MiSTer-devel/MiSTerLaggy_MiSTer/MiSTerLaggy.sv

//============================================================================
//
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
//============================================================================

module emu
(
	//Master input clock
	input         CLK_50M,

	//Async reset from top-level module.
	//Can be used as initial reset.
	input         RESET,

	//Must be passed to hps_io module
	inout  [48:0] HPS_BUS,

	//Base video clock. Usually equals to CLK_SYS.
	output        CLK_VIDEO,

	//Multiple resolutions are supported using different CE_PIXEL rates.
	//Must be based on CLK_VIDEO
	output        CE_PIXEL,

	//Video aspect ratio for HDMI. Most retro systems have ratio 4:3.
	//if VIDEO_ARX[12] or VIDEO_ARY[12] is set then [11:0] contains scaled size instead of aspect ratio.
	output [12:0] VIDEO_ARX,
	output [12:0] VIDEO_ARY,

	output  [7:0] VGA_R,
	output  [7:0] VGA_G,
	output  [7:0] VGA_B,
	output        VGA_HS,
	output        VGA_VS,
	output        VGA_DE,    // = ~(VBlank | HBlank)
	output        VGA_F1,
	output [1:0]  VGA_SL,
	output        VGA_SCALER, // Force VGA scaler
	output        VGA_DISABLE, // analog out is off

	input  [11:0] HDMI_WIDTH,
	input  [11:0] HDMI_HEIGHT,
	output        HDMI_FREEZE,
	output        HDMI_BLACKOUT,

`ifdef MISTER_FB
	// Use framebuffer in DDRAM
	// FB_FORMAT:
	//    [2:0] : 011=8bpp(palette) 100=16bpp 101=24bpp 110=32bpp
	//    [3]   : 0=16bits 565 1=16bits 1555
	//    [4]   : 0=RGB  1=BGR (for 16/24/32 modes)
	//
	// FB_STRIDE either 0 (rounded to 256 bytes) or multiple of pixel size (in bytes)
	output        FB_EN,
	output  [4:0] FB_FORMAT,
	output [11:0] FB_WIDTH,
	output [11:0] FB_HEIGHT,
	output [31:0] FB_BASE,
	output [13:0] FB_STRIDE,
	input         FB_VBL,
	input         FB_LL,
	output        FB_FORCE_BLANK,

`ifdef MISTER_FB_PALETTE
	// Palette control for 8bit modes.
	// Ignored for other video modes.
	output        FB_PAL_CLK,
	output  [7:0] FB_PAL_ADDR,
	output [23:0] FB_PAL_DOUT,
	input  [23:0] FB_PAL_DIN,
	output        FB_PAL_WR,
`endif
`endif

	output        LED_USER,  // 1 - ON, 0 - OFF.

	// b[1]: 0 - LED status is system status OR'd with b[0]
	//       1 - LED status is controled solely by b[0]
	// hint: supply 2'b00 to let the system control the LED.
	output  [1:0] LED_POWER,
	output  [1:0] LED_DISK,

	// I/O board button press simulation (active high)
	// b[1]: user button
	// b[0]: osd button
	output  [1:0] BUTTONS,

	input         CLK_AUDIO, // 24.576 MHz
	output [15:0] AUDIO_L,
	output [15:0] AUDIO_R,
	output        AUDIO_S,   // 1 - signed audio samples, 0 - unsigned
	output  [1:0] AUDIO_MIX, // 0 - no mix, 1 - 25%, 2 - 50%, 3 - 100% (mono)

	//ADC
	inout   [3:0] ADC_BUS,

	//SD-SPI
	output        SD_SCK,
	output        SD_MOSI,
	input         SD_MISO,
	output        SD_CS,
	input         SD_CD,

	//High latency DDR3 RAM interface
	//Use for non-critical time purposes
	output        DDRAM_CLK,
	input         DDRAM_BUSY,
	output  [7:0] DDRAM_BURSTCNT,
	output [28:0] DDRAM_ADDR,
	input  [63:0] DDRAM_DOUT,
	input         DDRAM_DOUT_READY,
	output        DDRAM_RD,
	output [63:0] DDRAM_DIN,
	output  [7:0] DDRAM_BE,
	output        DDRAM_WE,

	//SDRAM interface with lower latency
	output        SDRAM_CLK,
	output        SDRAM_CKE,
	output [12:0] SDRAM_A,
	output  [1:0] SDRAM_BA,
	inout  [15:0] SDRAM_DQ,
	output        SDRAM_DQML,
	output        SDRAM_DQMH,
	output        SDRAM_nCS,
	output        SDRAM_nCAS,
	output        SDRAM_nRAS,
	output        SDRAM_nWE,

`ifdef MISTER_DUAL_SDRAM
	//Secondary SDRAM
	//Set all output SDRAM_* signals to Z ASAP if SDRAM2_EN is 0
	input         SDRAM2_EN,
	output        SDRAM2_CLK,
	output [12:0] SDRAM2_A,
	output  [1:0] SDRAM2_BA,
	inout  [15:0] SDRAM2_DQ,
	output        SDRAM2_nCS,
	output        SDRAM2_nCAS,
	output        SDRAM2_nRAS,
	output        SDRAM2_nWE,
`endif

	input         UART_CTS,
	output        UART_RTS,
	input         UART_RXD,
	output        UART_TXD,
	output        UART_DTR,
	input         UART_DSR,

	// Open-drain User port.
	// 0 - D+/RX
	// 1 - D-/TX
	// 2..6 - USR2..USR6
	// Set USER_OUT to 1 to read from USER_IN.
	input   [6:0] USER_IN,
	output  [6:0] USER_OUT,

	input         OSD_STATUS,

	output        VIO_EN,
	output        VIO_STROBE,
	input  [15:0] VIO_DOUT,
	output [15:0] VIO_DIN,
	input  [15:0] VIO_CFG,

	input         HDMI_VBL
);

///////// Default values for ports not used in this core /////////

assign ADC_BUS  = 'Z;
assign {UART_RTS, UART_TXD, UART_DTR} = 0;
assign {SD_SCK, SD_MOSI, SD_CS} = 'Z;
assign {SDRAM_DQ, SDRAM_A, SDRAM_BA, SDRAM_CLK, SDRAM_CKE, SDRAM_DQML, SDRAM_DQMH, SDRAM_nWE, SDRAM_nCAS, SDRAM_nRAS, SDRAM_nCS} = 'Z;
assign {DDRAM_CLK, DDRAM_BURSTCNT, DDRAM_ADDR, DDRAM_DIN, DDRAM_BE, DDRAM_RD, DDRAM_WE} = '0;  

assign VGA_SL = 0;
assign VGA_F1 = 0;
assign VGA_SCALER  = 0;
assign VGA_DISABLE = 0;
assign HDMI_FREEZE = 0;
assign HDMI_BLACKOUT = 0;

assign AUDIO_S = 0;
assign AUDIO_L = 0;
assign AUDIO_R = 0;
assign AUDIO_MIX = 0;

assign LED_DISK = 0;
assign LED_POWER = 0;
assign BUTTONS = 0;

//////////////////////////////////////////////////////////////////

`include "build_id.v" 
localparam CONF_STR = {
	"MiSTerLaggy;;",
	"FC0,BIN,Load CPU ROM;",
	"-;",
	"T[0],Reset;",
	"J1,Ok,Back,Menu;",
	"jn,A,B,Start;",
	"V,v",`BUILD_DATE 
};

wire forced_scandoubler;
wire   [1:0] buttons;
wire [127:0] status;
wire  [10:0] ps2_key;
wire  [31:0] gamepad;

wire ioctl_download, ioctl_wr;
wire [15:0] ioctl_index, ioctl_dout;
wire [26:0] ioctl_addr;
wire new_vmode;

hps_io #(.CONF_STR(CONF_STR), .WIDE(1)) hps_io
(
	.clk_sys(clk_sys),
	.HPS_BUS(HPS_BUS),
	.gamma_bus(),

	.forced_scandoubler(forced_scandoubler),

	.buttons(buttons),
	.status(status),
	.status_menumask({status[5]}),

	.joystick_0(gamepad),
	
	.ps2_key(ps2_key),

	.ioctl_download(ioctl_download),
	.ioctl_wr(ioctl_wr),
	.ioctl_index(ioctl_index),
	.ioctl_addr(ioctl_addr),
	.ioctl_dout(ioctl_dout),
	.ioctl_wait(0),

	.new_vmode(new_vmode)
);

///////////////////////   CLOCKS   ///////////////////////////////

wire clk_sys;

wire [63:0] reconfig_to_pll;
wire [63:0] reconfig_from_pll;
wire        cfg_waitrequest;
reg         cfg_write;
reg   [5:0] cfg_address;
reg  [31:0] cfg_data;

pll pll
(
	.refclk(CLK_50M),
	.rst(0),
	.outclk_0(clk_sys),
	.reconfig_from_pll(reconfig_from_pll),
	.reconfig_to_pll(reconfig_to_pll)
);

pll_cfg pll_cfg
(
	.mgmt_clk(CLK_50M),
	.mgmt_reset(0),
	.mgmt_waitrequest(cfg_waitrequest),
	.mgmt_read(0),
	.mgmt_readdata(),
	.mgmt_write(cfg_write),
	.mgmt_address(cfg_address),
	.mgmt_writedata(cfg_data),
	.reconfig_to_pll(reconfig_to_pll),
	.reconfig_from_pll(reconfig_from_pll)
);

wire [5:0] pll_addr;
wire [31:0] pll_value;
wire pll_busy;
wire pll_write;

reg pll_fifo_rdack = 0;
wire [5:0] pll_cfg_addr;
wire [31:0] pll_cfg_value;
wire pll_fifo_empty;

pll_fifo pll_fifo(
	.wrclk(clk_sys),
	.wrreq(pll_write),
	.wrfull(pll_busy),
	.data({2'b00, pll_addr, pll_value}),

	.rdclk(CLK_50M),
	.rdreq(pll_fifo_rdack),
	.q({pll_cfg_addr, pll_cfg_value}),
	.rdempty(pll_fifo_empty)
);

always_ff @(posedge CLK_50M) begin
	cfg_write <= 0;
	pll_fifo_rdack <= 0;

	if (~cfg_waitrequest & ~pll_fifo_empty) begin
		cfg_write <= 1;
		cfg_address <= pll_cfg_addr;
		cfg_data <= pll_cfg_value;
		pll_fifo_rdack <= 1;
	end
end

wire reset = RESET | status[0] | buttons[1] | ioctl_download;

wire HBlank;
wire HSync;
wire VBlank;
wire VSync;

system system
(
	.clk(clk_sys),
	.clk_50m(CLK_50M),

	.reset(reset),

	.ce_pixel(CE_PIXEL),

	.HBlank(HBlank),
	.HSync(HSync),
	.VBlank(VBlank),
	.VSync(VSync),

	.r(VGA_R),
	.g(VGA_G),
	.b(VGA_B),

	.gamepad(gamepad[15:0]),
	.user_out(USER_OUT),
	.user_in(USER_IN),

	.ioctl_download(ioctl_download),
	.ioctl_wr(ioctl_wr),
	.ioctl_index(ioctl_index),
	.ioctl_addr(ioctl_addr),
	.ioctl_dout(ioctl_dout),

	.vio_en(VIO_EN),
	.vio_strobe(VIO_STROBE),
	.vio_dout(VIO_DOUT),
	.vio_din(VIO_DIN),
	.vio_cfg(VIO_CFG),

	.hdmi_vblank(HDMI_VBL),

	.new_vmode(new_vmode),
	.arx(VIDEO_ARX),
	.ary(VIDEO_ARY),

	.pll_addr(pll_addr),
	.pll_value(pll_value),
	.pll_write(pll_write),
	.pll_busy(pll_busy)
);

assign CLK_VIDEO = clk_sys;

assign VGA_DE = ~(HBlank | VBlank);
assign VGA_HS = HSync;
assign VGA_VS = VSync;

reg  [26:0] act_cnt;
always @(posedge clk_sys) act_cnt <= act_cnt + 1'd1; 
assign LED_USER    = act_cnt[26]  ? act_cnt[25:18]  > act_cnt[7:0]  : act_cnt[25:18]  <= act_cnt[7:0];

endmodule
