MiSTer-devel/MiSTerLaggy_MiSTer/rtl/dpramv.sv

//============================================================================
//  Copyright (C) 2023 Martin Donlon
//
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
`timescale 1ns / 1ps

module dualport_ram #(
    parameter width = 8,
    parameter widthad = 10
) (
    // Port A
    input   wire                  clock_a,
    input   wire                  wren_a,
    input   wire    [widthad-1:0] address_a,
    input   wire    [width-1:0]   data_a,
    output  reg     [width-1:0]   q_a,

    // Port B
    input   wire                  clock_b,
    input   wire                  wren_b,
    input   wire    [widthad-1:0] address_b,
    input   wire    [width-1:0]   data_b,
    output  reg     [width-1:0]   q_b
);

// Shared ramory
reg [width-1:0] ram[(2**widthad)-1:0];

// Port A
always @(posedge clock_a) begin
    if (wren_a) begin
        ram[address_a] <= data_a;
        q_a <= data_a;
    end else begin
        q_a <= ram[address_a];
    end
end

// Port B
always @(posedge clock_b) begin
    if(wren_b) begin
        q_b      <= data_b;
        ram[address_b] <= data_b;
    end else begin
        q_b <= ram[address_b];
    end
end

endmodule

module singleport_ram #(
    parameter width = 8,
    parameter widthad = 10,
    parameter name = "NONE",
    parameter init_file = "UNUSED"
) (
    input   wire                   clock,
    input   wire                   wren,
    input   wire    [widthad-1:0]  address,
    input   wire    [width-1:0]    data,
    output  reg     [width-1:0]    q

);

altsyncram	altsyncram_component (
            .address_a (address),
            .clock0 (clock),
            .data_a (data),
            .wren_a (wren),
            .q_a (q),
            .aclr0 (1'b0),
            .aclr1 (1'b0),
            .address_b (1'b1),
            .addressstall_a (1'b0),
            .addressstall_b (1'b0),
            .byteena_a (1'b1),
            .byteena_b (1'b1),
            .clock1 (1'b1),
            .clocken0 (1'b1),
            .clocken1 (1'b1),
            .clocken2 (1'b1),
            .clocken3 (1'b1),
            .data_b (1'b1),
            .eccstatus (),
            .q_b (),
            .rden_a (1'b1),
            .rden_b (1'b1),
            .wren_b (1'b0));
defparam
    altsyncram_component.clock_enable_input_a = "BYPASS",
    altsyncram_component.clock_enable_output_a = "BYPASS",
    altsyncram_component.intended_device_family = "Cyclone V",
    altsyncram_component.lpm_hint = {"ENABLE_RUNTIME_MOD=YES,INSTANCE_NAME=", name},
    altsyncram_component.lpm_type = "altsyncram",
    altsyncram_component.init_file = init_file,
    altsyncram_component.numwords_a = 2**widthad,
    altsyncram_component.operation_mode = "SINGLE_PORT",
    altsyncram_component.outdata_aclr_a = "NONE",
    altsyncram_component.outdata_reg_a = "CLOCK0",
    altsyncram_component.power_up_uninitialized = "FALSE",
    altsyncram_component.ram_block_type = "M10K",
    altsyncram_component.read_during_write_mode_port_a = "DONT_CARE",
    altsyncram_component.widthad_a = widthad,
    altsyncram_component.width_a = width,
    altsyncram_component.width_byteena_a = 1;


endmodule

module singleport_unreg_ram #(
    parameter width = 8,
    parameter widthad = 10,
    parameter name = "NONE",
    parameter init_file = "UNUSED"
) (
    input   wire                   clock,
    input   wire                   wren,
    input   wire    [widthad-1:0]  address,
    input   wire    [width-1:0]    data,
    output  wire    [width-1:0]    q
);

altsyncram	altsyncram_component (
            .address_a (address),
            .clock0 (clock),
            .data_a (data),
            .wren_a (wren),
            .q_a (q),
            .aclr0 (1'b0),
            .aclr1 (1'b0),
            .address_b (1'b1),
            .addressstall_a (1'b0),
            .addressstall_b (1'b0),
            .byteena_a (1'b1),
            .byteena_b (1'b1),
            .clock1 (1'b1),
            .clocken0 (1'b1),
            .clocken1 (1'b1),
            .clocken2 (1'b1),
            .clocken3 (1'b1),
            .data_b (1'b1),
            .eccstatus (),
            .q_b (),
            .rden_a (1'b1),
            .rden_b (1'b1),
            .wren_b (1'b0));
defparam
    altsyncram_component.clock_enable_input_a = "BYPASS",
    altsyncram_component.clock_enable_output_a = "BYPASS",
    altsyncram_component.intended_device_family = "Cyclone V",
    altsyncram_component.lpm_hint = {"ENABLE_RUNTIME_MOD=YES,INSTANCE_NAME=", name},
    altsyncram_component.lpm_type = "altsyncram",
    altsyncram_component.init_file = init_file,
    altsyncram_component.numwords_a = 2**widthad,
    altsyncram_component.operation_mode = "SINGLE_PORT",
    altsyncram_component.outdata_aclr_a = "NONE",
    altsyncram_component.outdata_reg_a = "UNREGISTERED",
    altsyncram_component.power_up_uninitialized = "FALSE",
    altsyncram_component.ram_block_type = "M10K",
    altsyncram_component.read_during_write_mode_port_a = "DONT_CARE",
    altsyncram_component.widthad_a = widthad,
    altsyncram_component.width_a = width,
    altsyncram_component.width_byteena_a = 1;

endmodule

module dualport_unreg_ram #(
    parameter width = 8,
    parameter widthad = 10,
    parameter init_file = "UNUSED"
) (
    // Port A
    input   wire                  clock_a,
    input   wire                  wren_a,
    input   wire    [widthad-1:0] address_a,
    input   wire    [width-1:0]   data_a,
    output  wire    [width-1:0]   q_a,

    // Port B
    input   wire                  clock_b,
    input   wire                  wren_b,
    input   wire    [widthad-1:0] address_b,
    input   wire    [width-1:0]   data_b,
    output  wire    [width-1:0]   q_b
);
	altsyncram	altsyncram_component (
				.address_a (address_a),
				.address_b (address_b),
				.clock0 (clock_a),
				.clock1 (clock_b),
				.data_a (data_a),
				.data_b (data_b),
				.wren_a (wren_a),
				.wren_b (wren_b),
				.q_a (q_a),
				.q_b (q_b),
				.aclr0 (1'b0),
				.aclr1 (1'b0),
				.addressstall_a (1'b0),
				.addressstall_b (1'b0),
				.byteena_a (1'b1),
				.byteena_b (1'b1),
				.clocken0 (1'b1),
				.clocken1 (1'b1),
				.clocken2 (1'b1),
				.clocken3 (1'b1),
				.eccstatus (),
				.rden_a (1'b1),
				.rden_b (1'b1));
	defparam
		altsyncram_component.address_reg_b = "CLOCK1",
		altsyncram_component.clock_enable_input_a = "BYPASS",
		altsyncram_component.clock_enable_input_b = "BYPASS",
		altsyncram_component.clock_enable_output_a = "BYPASS",
		altsyncram_component.clock_enable_output_b = "BYPASS",
		altsyncram_component.indata_reg_b = "CLOCK1",
		altsyncram_component.intended_device_family = "Cyclone V",
		altsyncram_component.lpm_type = "altsyncram",
        altsyncram_component.init_file = init_file,
		altsyncram_component.numwords_a = 2**widthad,
		altsyncram_component.numwords_b = 2**widthad,
		altsyncram_component.operation_mode = "BIDIR_DUAL_PORT",
		altsyncram_component.outdata_aclr_a = "NONE",
		altsyncram_component.outdata_aclr_b = "NONE",
		altsyncram_component.outdata_reg_a = "UNREGISTERED",
		altsyncram_component.outdata_reg_b = "UNREGISTERED",
		altsyncram_component.power_up_uninitialized = "FALSE",
		altsyncram_component.ram_block_type = "M10K",
		altsyncram_component.read_during_write_mode_port_a = "NEW_DATA_NO_NBE_READ",
		altsyncram_component.read_during_write_mode_port_b = "NEW_DATA_NO_NBE_READ",
		altsyncram_component.widthad_a = widthad,
		altsyncram_component.widthad_b = widthad,
		altsyncram_component.width_a = width,
		altsyncram_component.width_b = width,
		altsyncram_component.width_byteena_a = 1,
		altsyncram_component.width_byteena_b = 1,
		altsyncram_component.wrcontrol_wraddress_reg_b = "CLOCK1";
endmodule
